nasu8151/HC4/extra/spice0.png

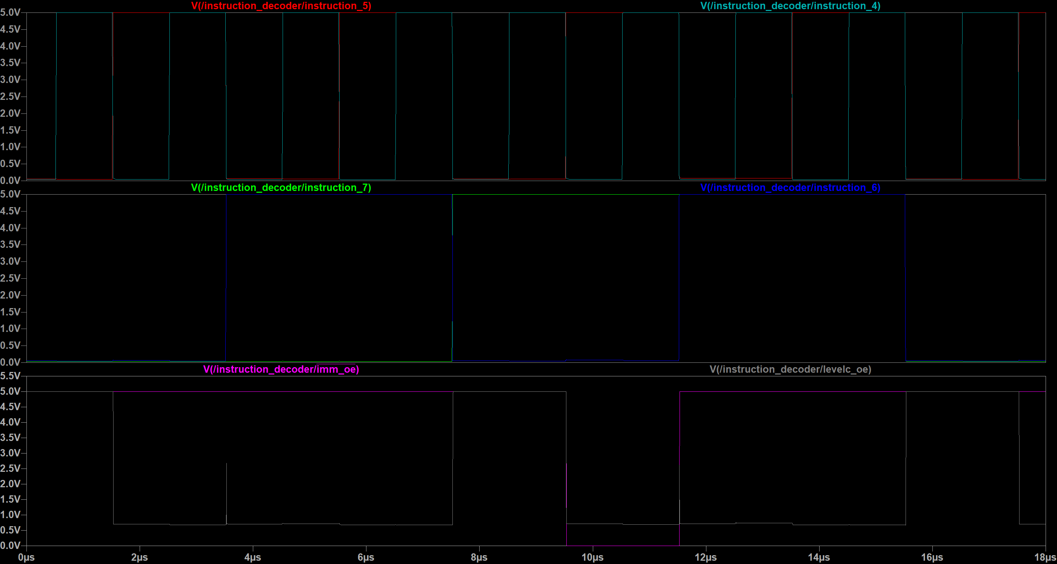
extra/spice0.png
