nasu8151/HC4/extra/spice1.png

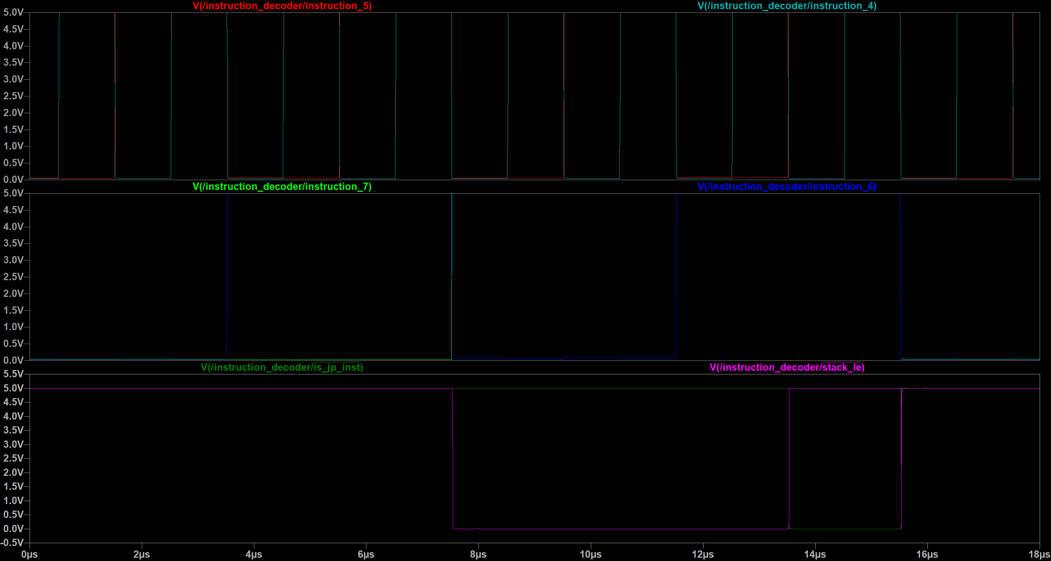
extra/spice1.png
