nasu8151/HC4/HC4_KiCad/sim/test04.asc

U1: 74hc04a
V1: voltage; 5
V2: voltage; PULSE(0 5 50n 5n 5n 50n 100n)
Named nets: 0
.tran 0 1m 0 1n
.lib C:\\Users\\senas\\AppData\\Local\\LTspice\\lib\\sub\\mysub\\74hc_full.lib
