nasu8151/HC4/HC4_KiCad/sim/test32.asc

U1: 74hc32a
V1: voltage; PULSE(0 5 1u 1n 1n 1m 2m)
V2: voltage; PULSE(0 5 1u 1n 1n 2m 4m)
Named nets: 0, out, out2, out3, out4
.lib 74hc_full.lib
.param vcc=5 tripdt=1n speed=1
.tran 0 10m 0 1u
