nasu8151/HC4/HC4_KiCad/sim/HC4_KiCad_tb.cir

.title KiCad schematic
.include "C:/Users/senas/Documents/shibaura/DGK/CPU/HC4/HC4_KiCad/sim/74hc.lib"
.include "C:/Users/senas/Documents/shibaura/DGK/CPU/HC4/HC4_KiCad/sim/74hc_full.lib"
.include "C:/Users/senas/Documents/shibaura/DGK/CPU/HC4/HC4_KiCad/sim/cd4000.lib"
.include "C:/Users/senas/Documents/shibaura/DGK/CPU/HC4/HC4_KiCad/sim/r_array.lib"
.model __D12 D
.model __D14 D
.model __D22 D
.model __D18 D
.model __D5 D
.model __D10 D
.model __D2 D
.model __D6 D
.model __D3 D
.model __D7 D
.model __D15 D
.model __D26 D
.model __D23 D
.model __D11 D
.model __D16 D
.model __D24 D
.model __D28 D
.model __D20 D
.model __D34 D
.model __D38 D
.model __D33 D
.model __D30 D
.model __D31 D
.model __D35 D
.model __D39 D
.param VCC=5 speed=1 tripdt=1n VDD={VCC}
.tran 0 260u 0 250n
V2 CLK 0 PULSE( 0 {VCC} 500n 2n 2n 500n 1u ) 
V1 VCC 0 DC 5 
XIC1 VCC VCC VCC VCC CLK unconnected-_IC1-A-Pad3_ unconnected-_IC1-B-Pad4_ unconnected-_IC1-C-Pad5_ unconnected-_IC1-D-Pad6_ /instruction_decoder/Instruction_4 /instruction_decoder/Instruction_5 /instruction_decoder/Instruction_6 /instruction_decoder/Instruction_7 unconnected-_IC1-CO-Pad15_ VCC 0 74HC161
D12 /instruction_decoder/MEMMode /instruction_decoder/_i4 __D12
XRN7 VCC Net-_D1-A_ Net-_D5-A_ /instruction_decoder/MEMMode /instruction_decoder/I0a Net-_D17-A_ Net-_D21-A_ Net-_D25-A_ Net-_D29-A_ RES_ARRAY_BUSSED
D14 /instruction_decoder/I0a /instruction_decoder/_i6 __D14
D22 Net-_D21-A_ /instruction_decoder/Instruction_6 __D22
D18 Net-_D17-A_ /instruction_decoder/_i6 __D18
XIC8 Net-_D17-A_ Net-_D17-A_ Net-_D21-A_ Net-_D21-A_ /instruction_decoder/I1a VCC 0 CD4002B
XIC3 VCC VCC unconnected-_IC3-Pad3_ /instruction_decoder/_i7 Net-_D5-A_ /instruction_decoder/_STACK_LE 0 /instruction_decoder/I2a /instruction_decoder/_i5 Net-_D25-A_ /instruction_decoder/I3a /instruction_decoder/Instruction_4 Net-_D29-A_ VCC 74hc32a
D5 Net-_D5-A_ /instruction_decoder/Instruction_7 __D5
D10 /instruction_decoder/MEMMode /instruction_decoder/_i6 __D10
D2 Net-_D1-A_ /instruction_decoder/_i6 __D2
D6 Net-_D5-A_ /instruction_decoder/Instruction_6 __D6
XIC5 Net-_D1-A_ /instruction_decoder/_i7 /instruction_decoder/_Carry_EN Net-_D1-A_ /instruction_decoder/Instruction_7 /instruction_decoder/_Imm_OE 0 /instruction_decoder/_RAM_RD /instruction_decoder/READ CLK /instruction_decoder/_RAM_WR /instruction_decoder/_i7 CLK VCC 74hc00a
XIC4 /instruction_decoder/Instruction_7 /instruction_decoder/_i7 /instruction_decoder/Instruction_5 /instruction_decoder/_i5 VCC unconnected-_IC4-Pad6_ 0 /instruction_decoder/_is_JP_inst Net-_D5-A_ /instruction_decoder/_i4 /instruction_decoder/Instruction_4 /instruction_decoder/_i6 /instruction_decoder/Instruction_6 VCC 74hc04a
D3 Net-_D1-A_ /instruction_decoder/Instruction_5 __D3
D7 Net-_D5-A_ /instruction_decoder/Instruction_5 __D7
D15 /instruction_decoder/I0a /instruction_decoder/Instruction_5 __D15
D26 Net-_D25-A_ /instruction_decoder/_i6 __D26
D23 Net-_D21-A_ /instruction_decoder/Instruction_5 __D23
D11 /instruction_decoder/MEMMode /instruction_decoder/_i5 __D11
D16 /instruction_decoder/I0a /instruction_decoder/_i4 __D16
D24 Net-_D21-A_ /instruction_decoder/_i4 __D24
D28 Net-_D25-A_ /instruction_decoder/Instruction_4 __D28
D20 Net-_D17-A_ /instruction_decoder/Instruction_4 __D20
CP7 VCC 0 0.1u
CP6 VCC 0 0.1u
CP4 VCC 0 0.1u
CP5 VCC 0 0.1u
CP3 VCC 0 0.1u
CP2 VCC 0 0.1u
CP1 VCC 0 0.1u
D34 /instruction_decoder/READ /instruction_decoder/_i6 __D34
D38 /instruction_decoder/LevelC_OE /instruction_decoder/_i6 __D38
D33 /instruction_decoder/READ /instruction_decoder/Instruction_7 __D33
R9 VCC /instruction_decoder/READ 10k
D30 Net-_D29-A_ /instruction_decoder/Instruction_6 __D30
R10 VCC /instruction_decoder/LevelC_OE 10k
D31 Net-_D29-A_ /instruction_decoder/Instruction_5 __D31
D35 /instruction_decoder/READ /instruction_decoder/_i5 __D35
D39 /instruction_decoder/LevelC_OE /instruction_decoder/_i5 __D39
.end
